SiloCityLabs/Cuttlephone/docs/assets/images/og-image.png

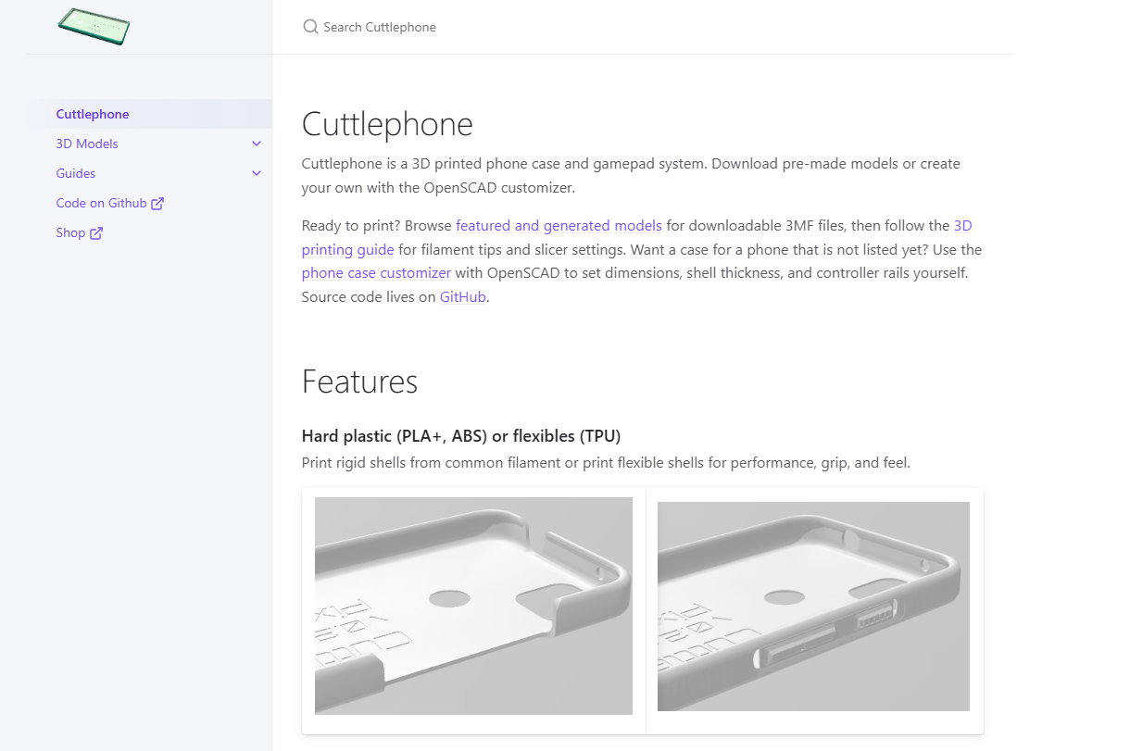
docs/assets/images/og-image.png
