SiloCityLabs/Cuttlephone/docs/assets/images/sia-head-512.png

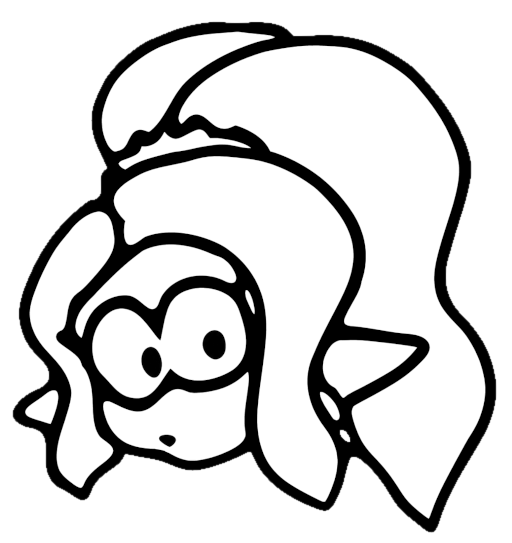
docs/assets/images/sia-head-512.png
