SiloCityLabs/Cuttlephone/docs/premade_models/Pixel 3a junglecat hard.3mf

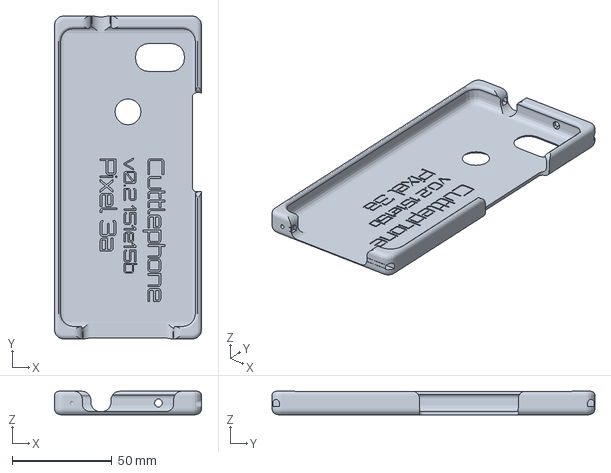
[picture p29: CAD file, 2021-12-20]
docs/premade_models/Pixel 3a junglecat hard.3mf
73.8 x 162.1 x 11.8 mm
