SiloCityLabs/Cuttlephone/docs/premade_models/Pixel 3 gamepad soft.3mf

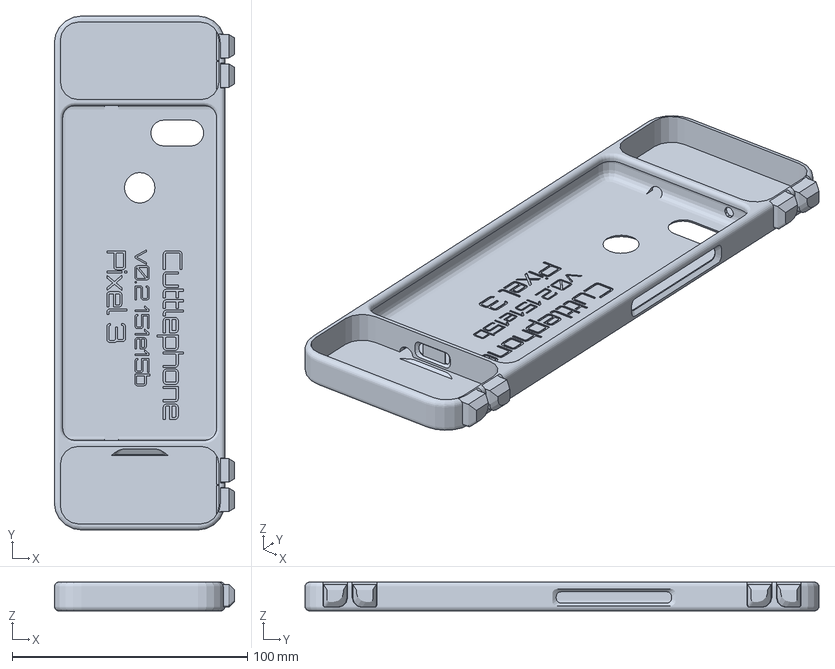
[picture p30: CAD file, 2021-12-20]
docs/premade_models/Pixel 3 gamepad soft.3mf
76.8 x 218.7 x 12.3 mm
