SiloCityLabs/Cuttlephone/docs/premade_models/Pixel 3 XL junglecat soft.3mf

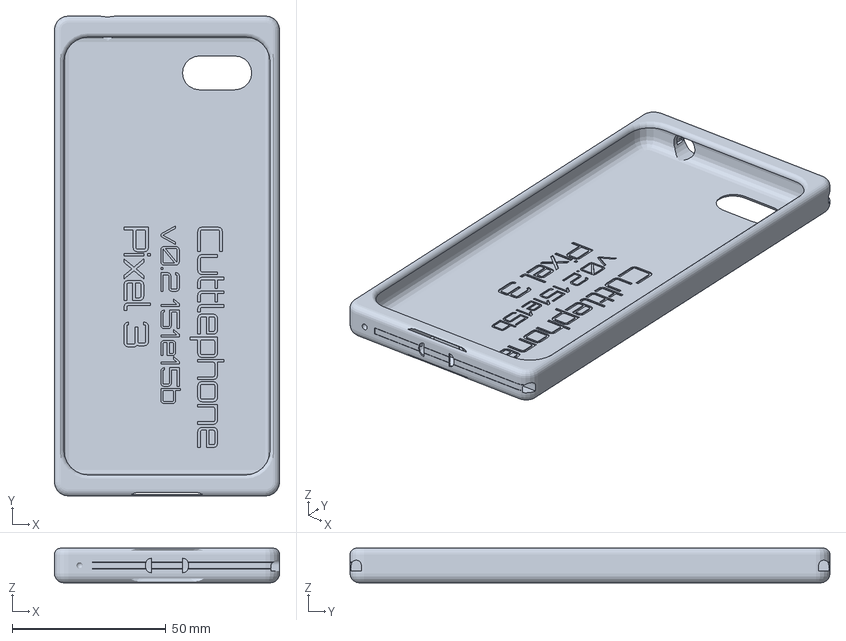
[picture p32: CAD file, 2021-12-20]
docs/premade_models/Pixel 3 XL junglecat soft.3mf
73.3 x 156.1 x 11.3 mm
