SiloCityLabs/Cuttlephone/docs/premade_models/Galaxy S9+ joycon hard.3mf

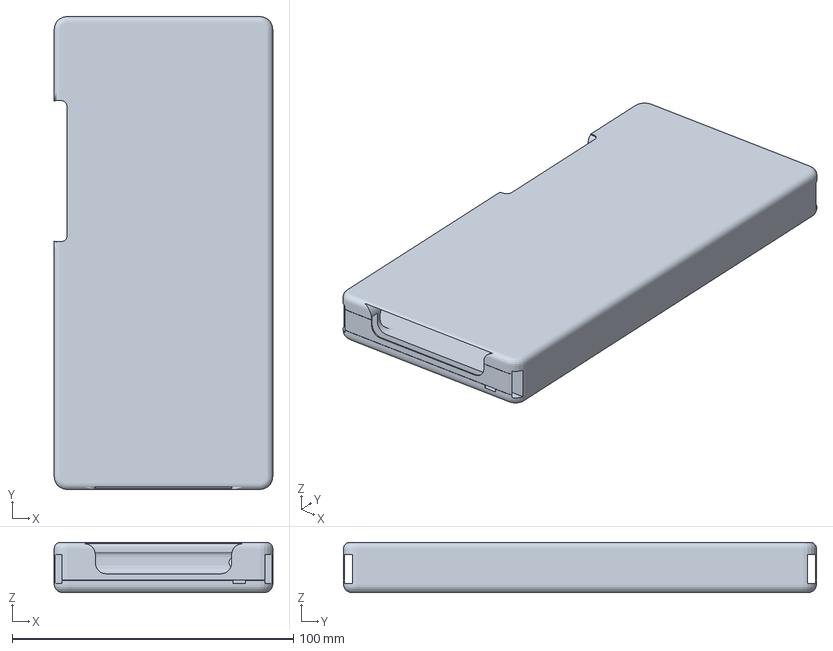
[picture p33: CAD file, 2021-12-20]
docs/premade_models/Galaxy S9+ joycon hard.3mf
77.7 x 168.1 x 17.8 mm
