SiloCityLabs/Cuttlephone/docs/premade_models/Pixel 3 joycon soft.3mf

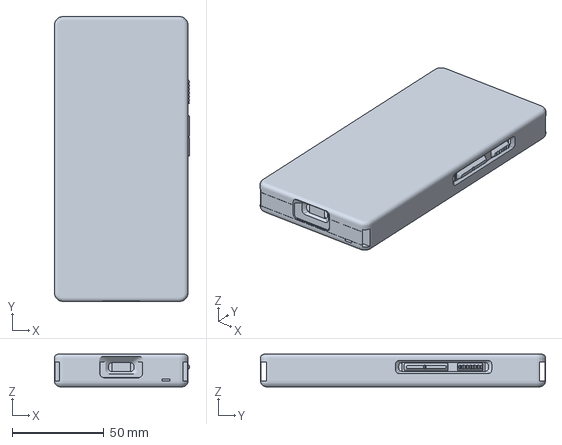
[picture p34: CAD file, 2021-12-20]
docs/premade_models/Pixel 3 joycon soft.3mf
73.5 x 155.1 x 17.8 mm
