SiloCityLabs/Cuttlephone/docs/premade_models/Galaxy S9+ phone case hard.3mf

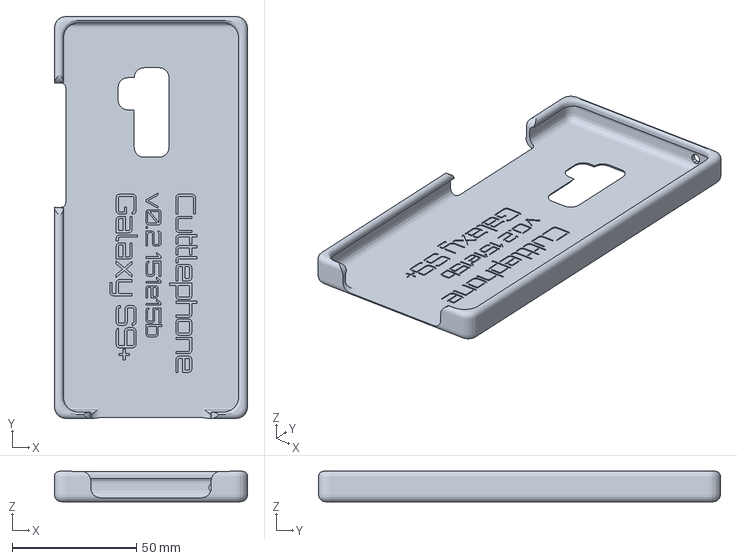
[picture p35: CAD file, 2021-12-20]
docs/premade_models/Galaxy S9+ phone case hard.3mf
77.7 x 161.7 x 12.3 mm
