SiloCityLabs/Cuttlephone/docs/premade_models/Pixel 3 XL gamepad hard.3mf

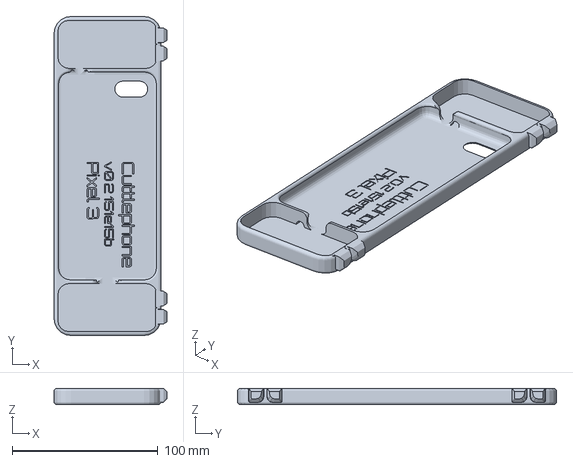
[picture p36: CAD file, 2021-12-20]
docs/premade_models/Pixel 3 XL gamepad hard.3mf
77.4 x 218.7 x 11.3 mm
