SiloCityLabs/Cuttlephone/docs/premade_models/Pixel 4a joycon hard.3mf

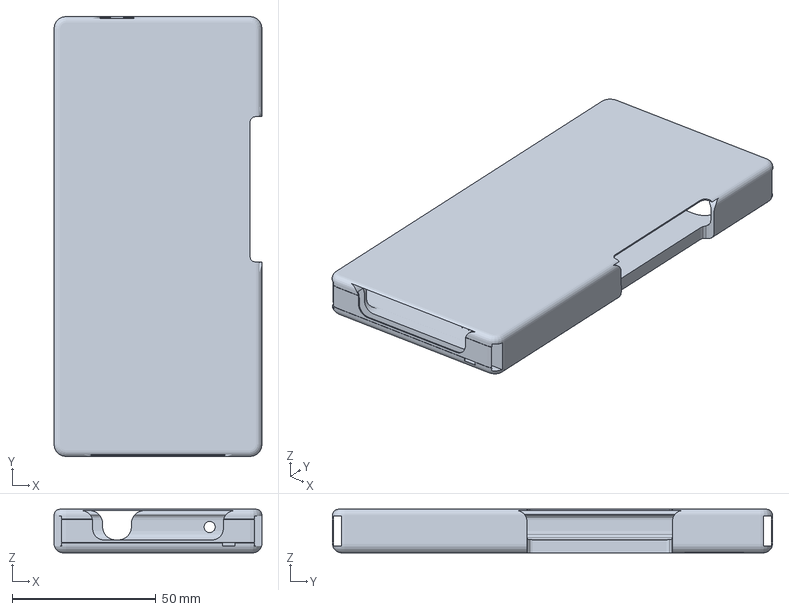
[picture p37: CAD file, 2021-12-20]
docs/premade_models/Pixel 4a joycon hard.3mf
72.3 x 153.0 x 15.2 mm
