SiloCityLabs/Cuttlephone/docs/premade_models/Pixel 3 XL junglecat hard.3mf

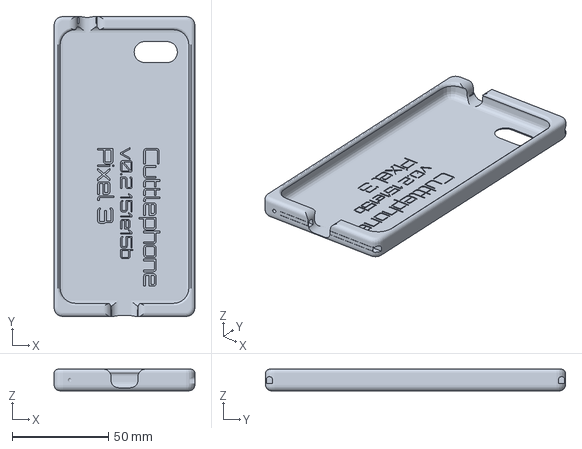
[picture p38: CAD file, 2021-12-20]
docs/premade_models/Pixel 3 XL junglecat hard.3mf
73.3 x 156.1 x 11.3 mm
