SiloCityLabs/Cuttlephone/docs/premade_models/Pixel 3 phone case soft.3mf

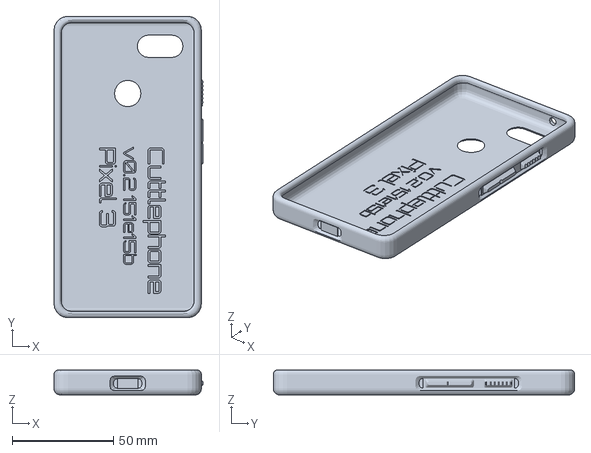
[picture p39: CAD file, 2021-12-20]
docs/premade_models/Pixel 3 phone case soft.3mf
73.5 x 148.7 x 12.3 mm
