SiloCityLabs/Cuttlephone/docs/premade_models/Pixel 3a joycon soft.3mf

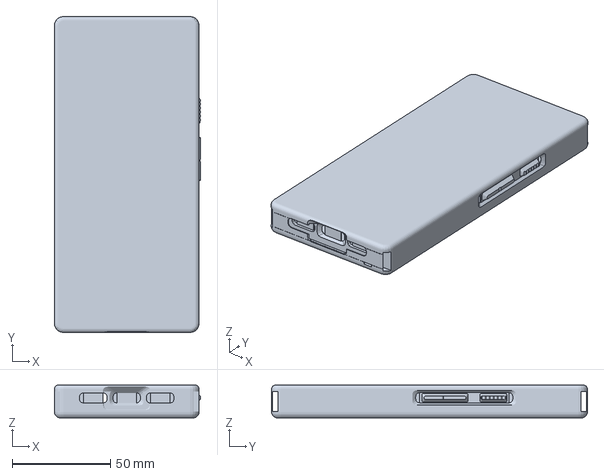
[picture p40: CAD file, 2021-12-20]
docs/premade_models/Pixel 3a joycon soft.3mf
74.6 x 161.1 x 16.8 mm
