SiloCityLabs/Cuttlephone/docs/premade_models/Pixel 4a phone case hard.3mf

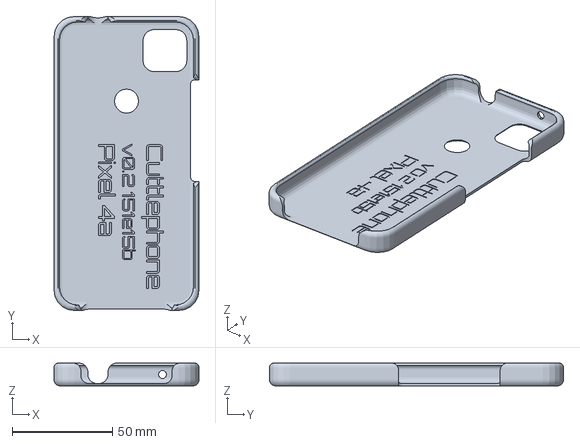
[picture p41: CAD file, 2021-12-20]
docs/premade_models/Pixel 4a phone case hard.3mf
72.3 x 146.6 x 11.4 mm
