SiloCityLabs/Cuttlephone/docs/premade_models/Pixel 3 XL joycon hard.3mf

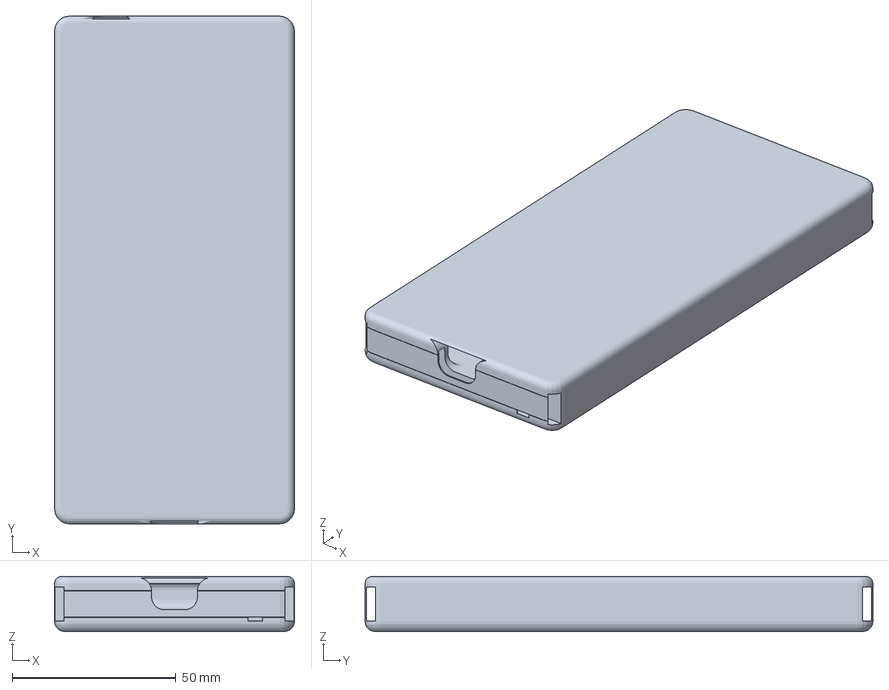
[picture p42: CAD file, 2021-12-20]
docs/premade_models/Pixel 3 XL joycon hard.3mf
73.3 x 155.1 x 16.8 mm
