SiloCityLabs/Cuttlephone/docs/premade_models/Galaxy S9+ joycon soft.3mf

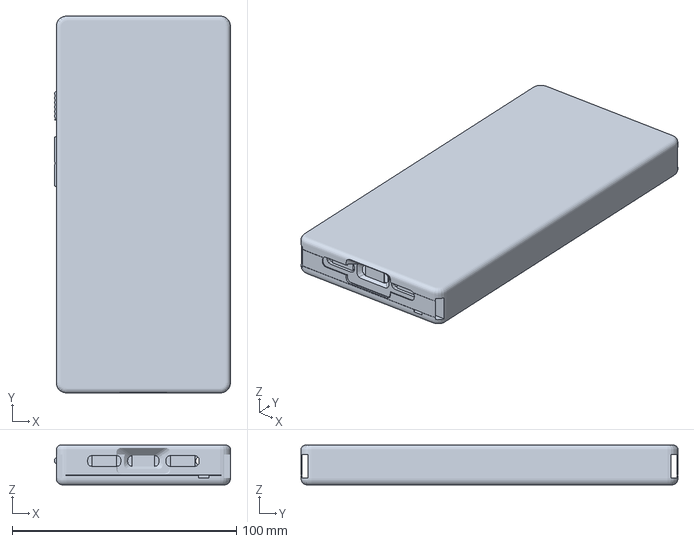
[picture p43: CAD file, 2021-12-20]
docs/premade_models/Galaxy S9+ joycon soft.3mf
78.5 x 168.1 x 17.8 mm
