SiloCityLabs/Cuttlephone/docs/premade_models/Pixel 3a junglecat soft.3mf

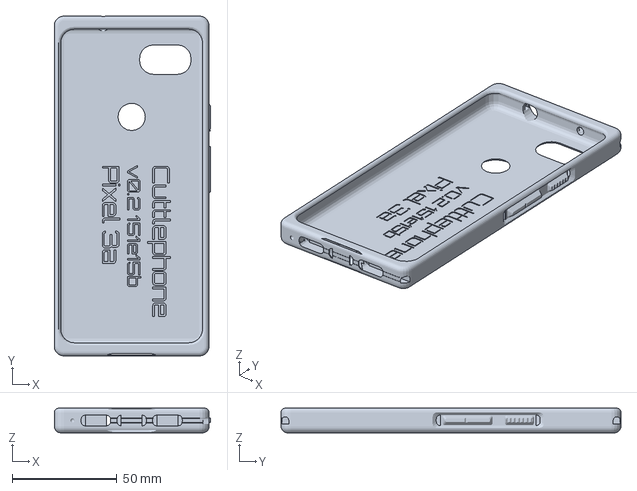
[picture p44: CAD file, 2021-12-20]
docs/premade_models/Pixel 3a junglecat soft.3mf
74.6 x 162.1 x 11.8 mm
