SiloCityLabs/Cuttlephone/docs/premade_models/Galaxy S9+ phone case soft.3mf

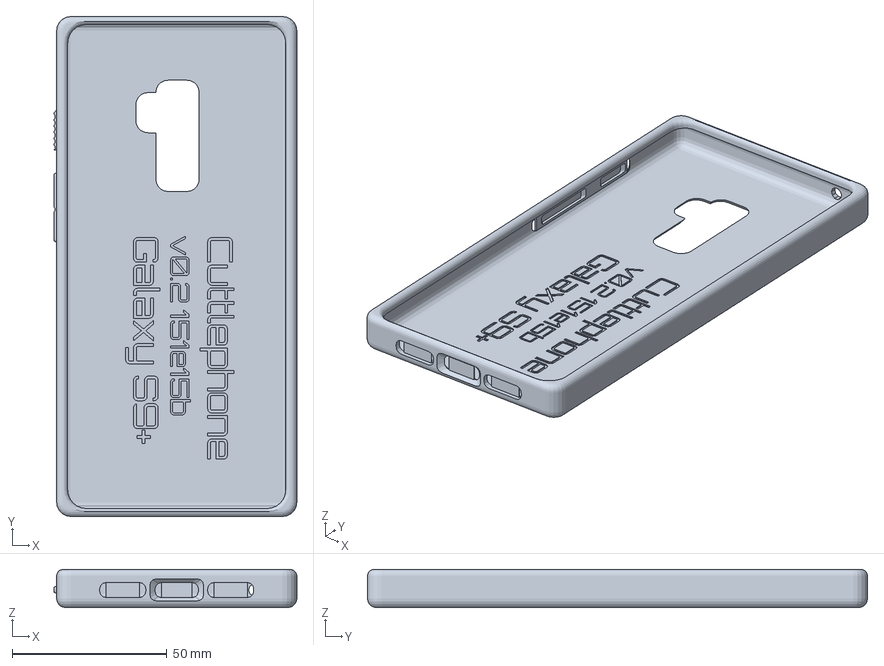
[picture p45: CAD file, 2021-12-20]
docs/premade_models/Galaxy S9+ phone case soft.3mf
78.5 x 161.7 x 12.3 mm
