SiloCityLabs/Cuttlephone/docs/premade_models/Pixel 3a phone case hard.3mf

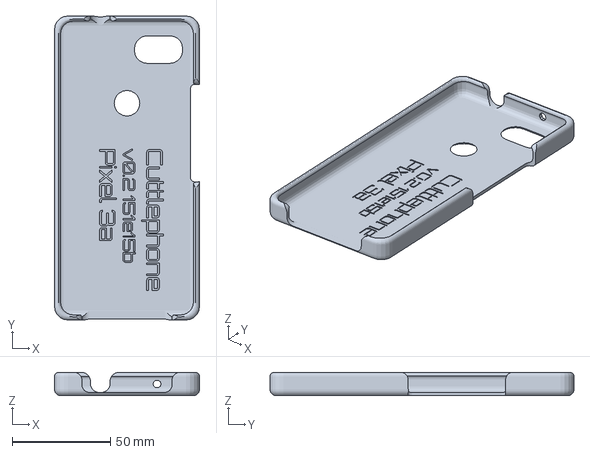
[picture p46: CAD file, 2021-12-20]
docs/premade_models/Pixel 3a phone case hard.3mf
73.8 x 154.7 x 11.8 mm
