SiloCityLabs/Cuttlephone/docs/premade_models/Pixel 3 phone case hard.3mf

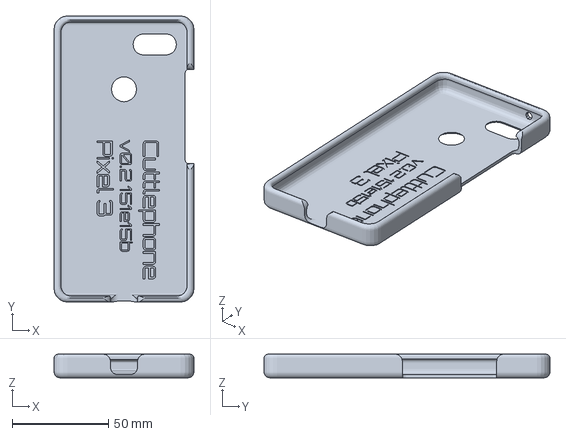
[picture p47: CAD file, 2021-12-20]
docs/premade_models/Pixel 3 phone case hard.3mf
72.7 x 148.7 x 12.3 mm
