SiloCityLabs/Cuttlephone/docs/premade_models/Pixel 3 gamepad hard.3mf

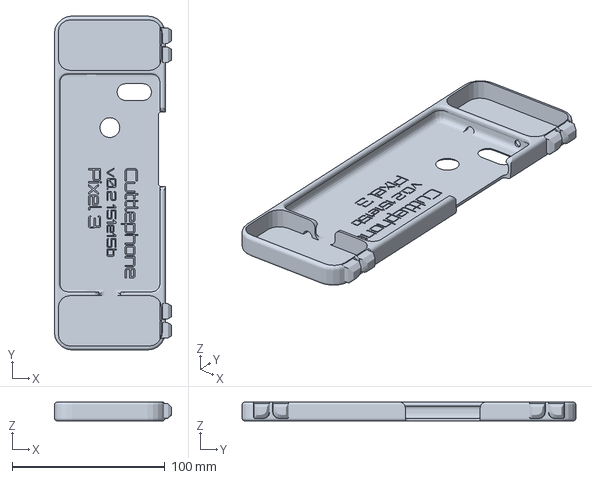
[picture p48: CAD file, 2021-12-20]
docs/premade_models/Pixel 3 gamepad hard.3mf
76.8 x 218.7 x 12.3 mm
