SiloCityLabs/Cuttlephone/docs/premade_models/Pixel 4a junglecat soft.3mf

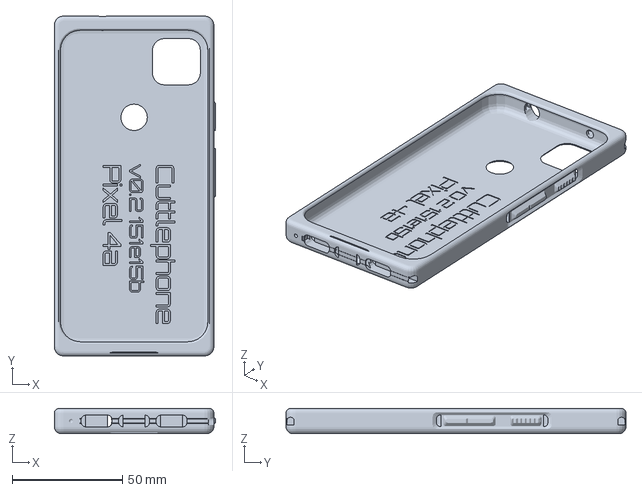
[picture p49: CAD file, 2021-12-20]
docs/premade_models/Pixel 4a junglecat soft.3mf
73.1 x 154.0 x 11.4 mm
