SiloCityLabs/Cuttlephone/docs/premade_models/Pixel 4a joycon soft.3mf

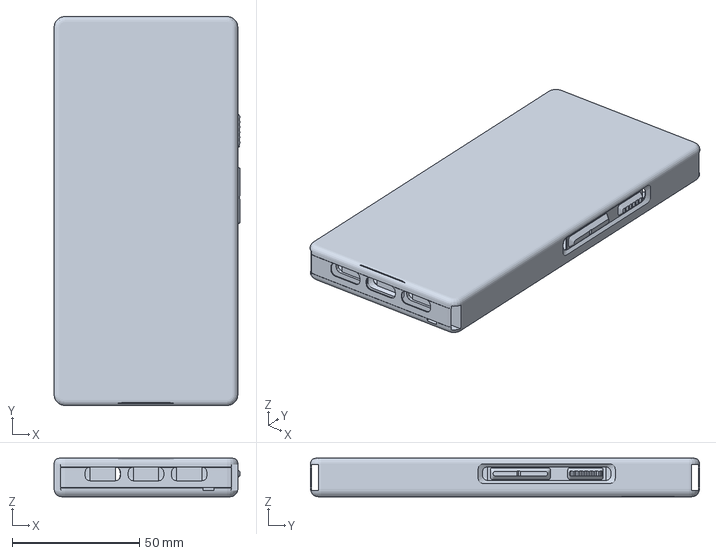
[picture p50: CAD file, 2021-12-20]
docs/premade_models/Pixel 4a joycon soft.3mf
73.1 x 153.0 x 15.2 mm
