SiloCityLabs/Cuttlephone/docs/premade_models/Galaxy S9+ gamepad soft.3mf

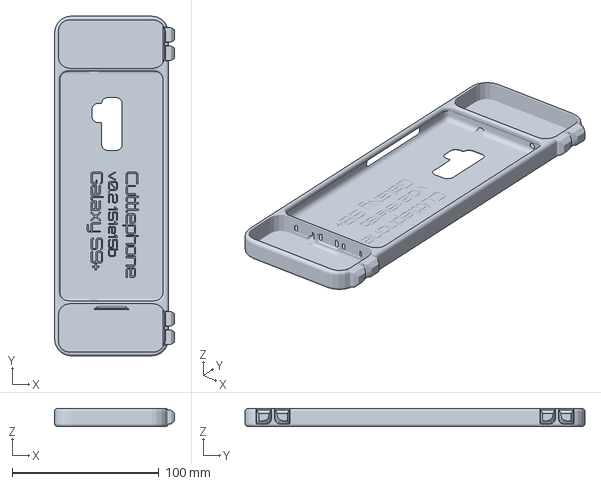
[picture p51: CAD file, 2021-12-20]
docs/premade_models/Galaxy S9+ gamepad soft.3mf
81.8 x 231.7 x 12.3 mm
