SiloCityLabs/Cuttlephone/docs/premade_models/Galaxy S9+ junglecat soft.3mf

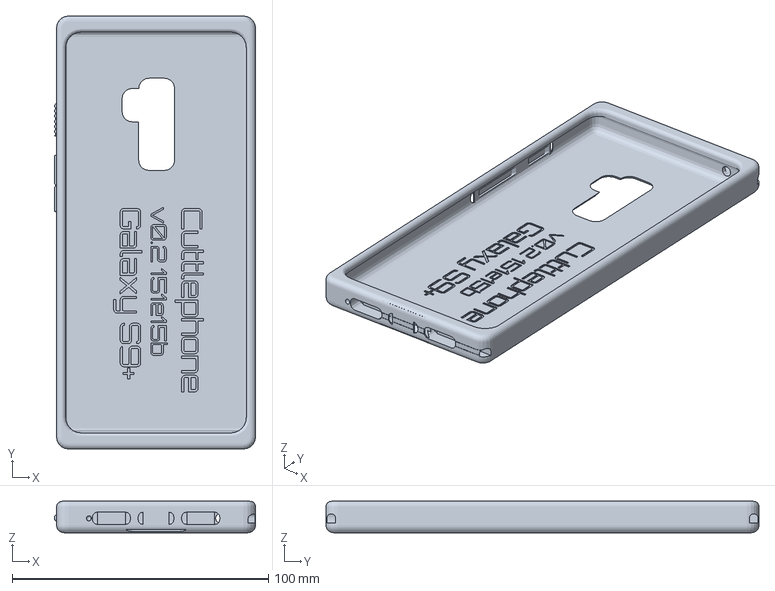
[picture p52: CAD file, 2021-12-20]
docs/premade_models/Galaxy S9+ junglecat soft.3mf
78.5 x 169.1 x 12.3 mm
