SiloCityLabs/Cuttlephone/docs/images/guides/generator-guide.png

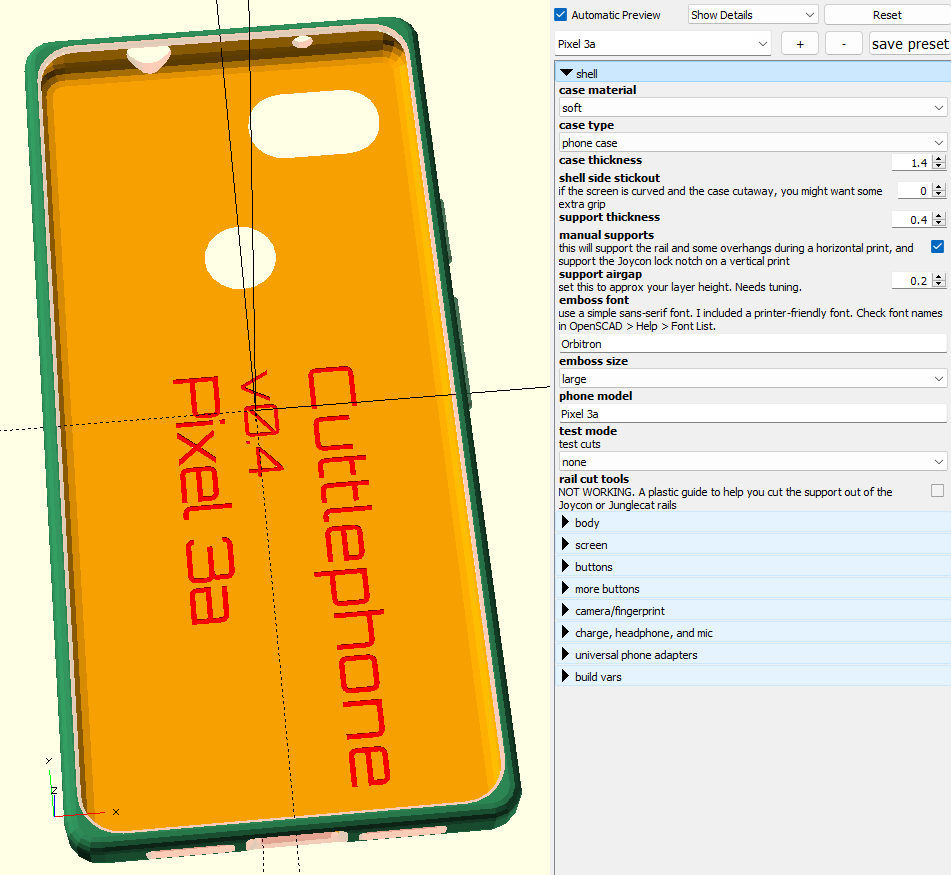
docs/images/guides/generator-guide.png
